raphaelmonnard/lbate-applaudimetre/software/receiver/spectacle.h

const int params[44][7] PROGMEM = {
    {100,100,100,100,100,100,1},
    {100,100,100,100,0,100,5},
    {0,0,0,0,0,0,7},
    {100,100,100,100,0,100,2},
    {100,100,100,100,0,100,3},
    {90,80,100,50,50,70,0},
    {90,80,100,50,50,70,4},
    {0,100,0,0,50,70,0},
    {100,0,0,0,50,70,0},
    {0,0,100,0,50,70,0},
    {0,0,0,100,50,15,0},
    {90,80,100,50,50,90,0},
    {100,100,100,100,100,100,8},
    {90,80,100,50,50,50,0},
    {100,100,100,100,50,60,0},
    {100,100,20,100,50,80,0},
    {30,30,100,20,50,90,0},
    {90,80,100,50,50,100,0},
    {80,90,100,50,50,90,0},
    {90,80,100,50,50,90,0},
    {80,80,100,50,50,90,0},
    {80,60,100,80,50,90,0},
    {90,90,100,90,50,90,0},
    {90,90,30,90,50,80,0},
    {80,80,100,60,50,10,5},
    {100,80,80,100,50,90,0},
    {80,80,100,80,50,90,0},
    {0,100,0,0,50,80,0},
    {100,0,0,0,50,60,0},
    {0,0,0,100,50,10,0},
    {0,0,100,0,50,100,0},
    {80,100,80,50,50,90,0},
    {100,80,100,50,50,90,0},
    {0,100,0,0,50,90,0},
    {0,0,0,100,50,90,0},
    {100,0,0,0,50,90,0},
    {0,0,100,0,50,20,0},
    {100,80,90,70,50,90,0},
    {0,0,0,0,0,0,4},
    {100,100,100,100,50,100,0},
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
};

const char desc_0[] PROGMEM = "Test intensité LED";
const char desc_1[] PROGMEM = "Test sensibilité du micro";
const char desc_2[] PROGMEM = "Pause";
const char desc_3[] PROGMEM = "Introduction";
const char desc_4[] PROGMEM = "The way you look tonight - avant solo sax";
const char desc_5[] PROGMEM = "The way you look tonight - fin";
const char desc_6[] PROGMEM = "Et en plus, l’applaudimètre fonctionne... c’est super !";
const char desc_7[] PROGMEM = "En bleu, notre guitariste : Jean-Baptiste De La Touche...";
const char desc_8[] PROGMEM = "En vert, notre saxophoniste : Charles Edouard von Bourdon...";
const char desc_9[] PROGMEM = "Et en rose, notre chanteue : Lady Bee !";
const char desc_10[] PROGMEM = "Et en jaune, notre contrebassiste : Sammy l’Asticot";
const char desc_11[] PROGMEM = "Vous avez compris ?";
const char desc_12[] PROGMEM = "He Ho !";
const char desc_13[] PROGMEM = "Swingy Lady";
const char desc_14[] PROGMEM = "Vous l’avez trouvée comment notre chanson ?";
const char desc_15[] PROGMEM = "Et nos musiciens, vous les avez trouvé comment ?";
const char desc_16[] PROGMEM = "Et notre chanteuse ? Elle est comment ?";
const char desc_17[] PROGMEM = "Don’t Get Around Much Anymore";
const char desc_18[] PROGMEM = "En retards";
const char desc_19[] PROGMEM = "Perhaps";
const char desc_20[] PROGMEM = "No moon at all";
const char desc_21[] PROGMEM = "Makin’ Whoopee";
const char desc_22[] PROGMEM = "Jeunes mariés / papa / maman / ...";
const char desc_23[] PROGMEM = "Sunday Morning Blues";
const char desc_24[] PROGMEM = "St. James Infirmary";
const char desc_25[] PROGMEM = "Devil May care";
const char desc_26[] PROGMEM = "Le temps du muguet";
const char desc_27[] PROGMEM = "Allez les fans de l’été, on applaudit !.";
const char desc_28[] PROGMEM = "Maintenant, on applaudit pour l’automne !";
const char desc_29[] PROGMEM = "Qui applaudit l’hiver ?";
const char desc_30[] PROGMEM = "Alors, qui vote pour le printemps ?!";
const char desc_31[] PROGMEM = "Lullaby of Birdland";
const char desc_32[] PROGMEM = "Poupette song";
const char desc_33[] PROGMEM = "On applaudit pour l’oiseau ?";
const char desc_34[] PROGMEM = "qui lui a brisé le cœur ?";
const char desc_35[] PROGMEM = "sur le canapé pour être intégré à sa famille humaine !";
const char desc_36[] PROGMEM = "lâcheuse de grands ours amoureux et voleuse de canapés !";
const char desc_37[] PROGMEM = "Miss Ceile’s Blues";
const char desc_38[] PROGMEM = "Coup de téléphone";
const char desc_39[] PROGMEM = "Vous avez eu du plaisir ?";
const char desc_40[] PROGMEM = "Péter l'applaudimètre";
const char desc_41[] PROGMEM = "Love me or Leave me";
const char desc_42[] PROGMEM = "He Ho !";
const char desc_43[] PROGMEM = "----- FIN -----";

const char *const desc[] PROGMEM = {
  desc_0,
  desc_1,
  desc_2,
  desc_3,
  desc_4,
  desc_5,
  desc_6,
  desc_7,
  desc_8,
  desc_9,
  desc_10,
  desc_11,
  desc_12,
  desc_13,
  desc_14,
  desc_15,
  desc_16,
  desc_17,
  desc_18,
  desc_19,
  desc_20,
  desc_21,
  desc_22,
  desc_23,
  desc_24,
  desc_25,
  desc_26,
  desc_27,
  desc_28,
  desc_29,
  desc_30,
  desc_31,
  desc_32,
  desc_33,
  desc_34,
  desc_35,
  desc_36,
  desc_37,
  desc_38,
  desc_39,
  desc_40,
  desc_41,
  desc_42,
  desc_43
};
